CapnKernel/doodad/kicad/doodad.sch

## KiCad design kicad/doodad.sch (2011-05-03)

Schematic: doodad.sch

Parts:
C1, C2, C3, C4: 100n
C5, C6: 18p
C7: 4u7
D1, D2: 3.6V
FUNC1, FUNC2: GS4
IC1: ATMEGA168PA-AU; TQFN32
JP17: RESET
JP18: ADC7
JP19: EXPAND
JP20: 5V
JP21: ⏚
JP22: USB_2; USB_PCB_FINGERS
L1: 10mH
LED1, LED2, LED3, LED4, LED5, LED6, LED7, LED8, LED9, LED10: GREEN
LED11: YELLOW
LED12, LED13, LED14, LED15, LED16: RED
Q1: CRYSTAL
R1, R2, R3, R4, R5, R6, R7, R8, R9, R10, R11: 180R
R12, R13, R14, R15, R16: 360R
R17, R18, R24: 10k
R19, R20, R23, R26: 0R
R21: 1k5
R22, R25: 68R
S1: BOOT
